MartinRusk/G1000/design/Panel/Gear handle.3mf

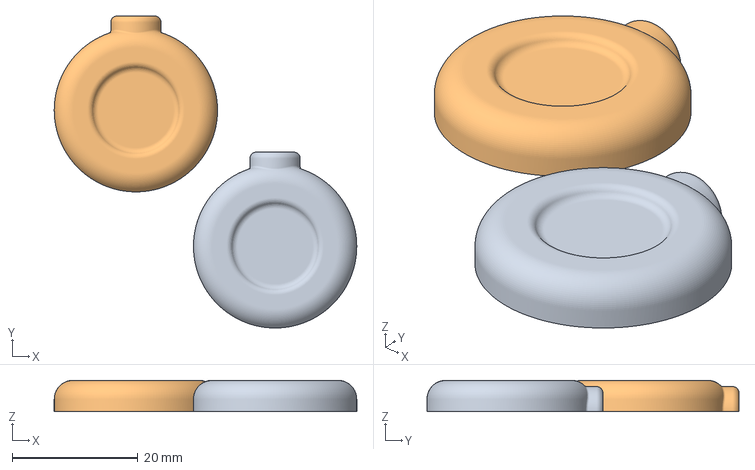
[picture p17: CAD file, 2022-03-11]
design/Panel/Gear handle.3mf
48.2 x 49.7 x 5.00 mm
Gear handle large left.stl
Gear handle large right.stl
