MartinRusk/G1000/design/Bezel/Bezel Top.3mf

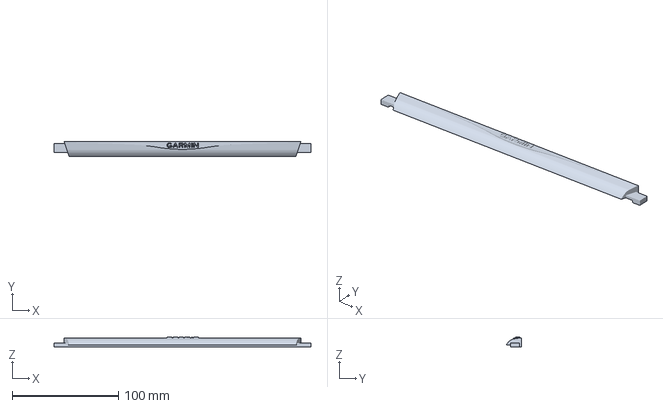
[picture p18: CAD file, 2022-01-23]
design/Bezel/Bezel Top.3mf
241.4 x 14.4 x 9.72 mm
