MartinRusk/G1000/design/Buttons/Buttons KEY.3mf

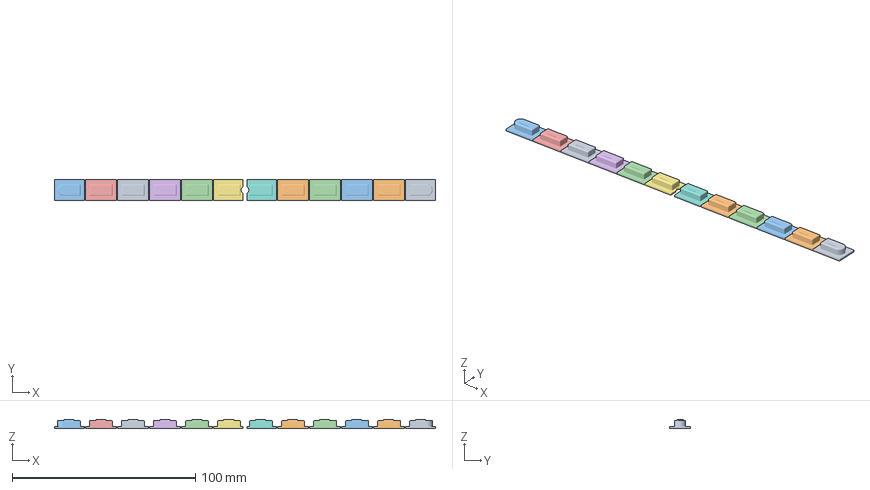
[picture p19: CAD file, 2022-01-23]
design/Buttons/Buttons KEY.3mf
208.1 x 11.6 x 4.67 mm
Buttons KEY_1
Buttons KEY_2
Buttons KEY_3
Buttons KEY_4
Buttons KEY_5
Buttons KEY_6
Buttons KEY_7
Buttons KEY_8
Buttons KEY_9
Buttons KEY_10
Buttons KEY_11
Buttons KEY_12
