MartinRusk/G1000/design/Buttons/STL/KEY 12.stl

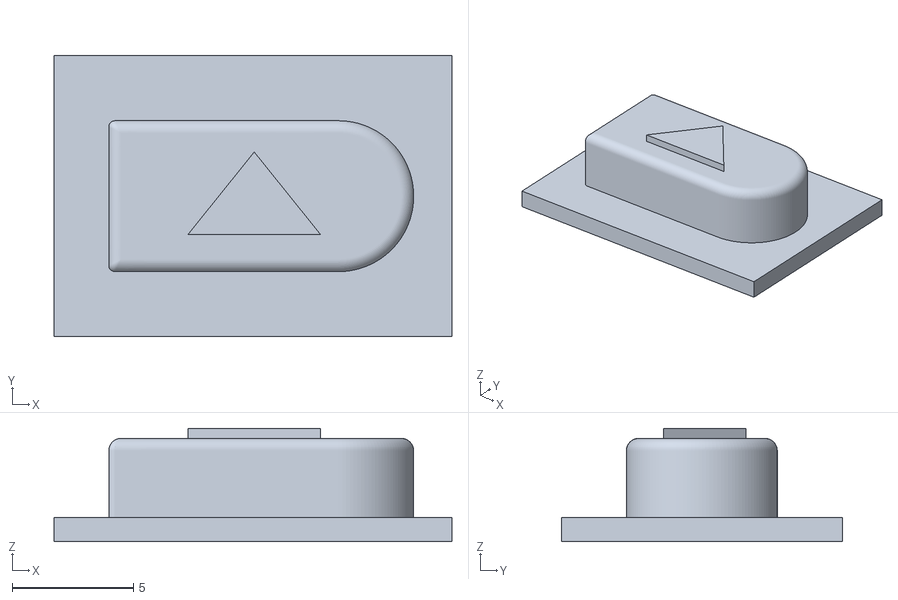
[picture p20: CAD file, 2022-04-21]
design/Buttons/STL/KEY 12.stl
16.4 x 11.6 x 4.67
