MartinRusk/G1000/design/Display/Display Frame VS104T.3mf

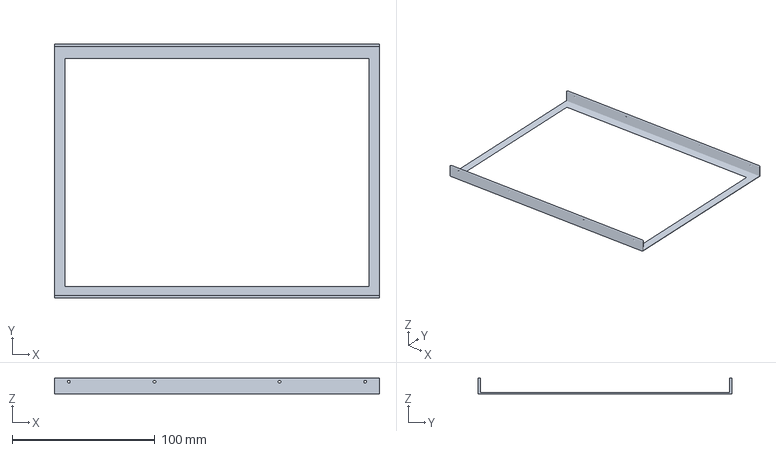
[picture p21: CAD file, 2022-01-28]
design/Display/Display Frame VS104T.3mf
227.6 x 177.7 x 11.0 mm
