MartinRusk/G1000/design/Encoders/Rudder Trim Knob.3mf

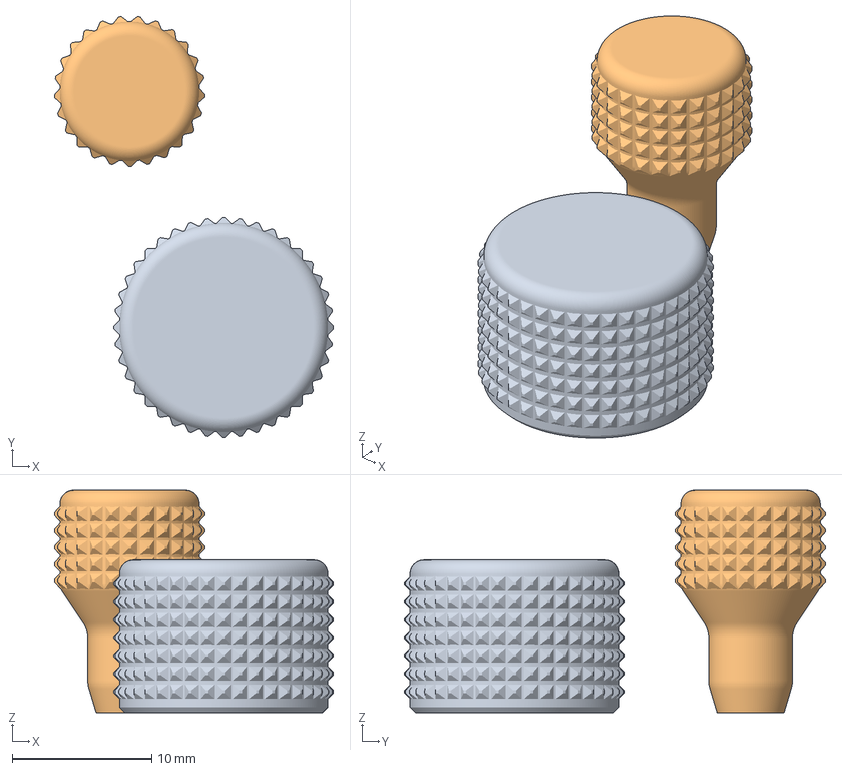
[picture p22: CAD file, 2022-03-11]
design/Encoders/Rudder Trim Knob.3mf
20.1 x 30.2 x 16.0 mm
Trim Knob knurled.stl
Range Pan Knob knurled new.stl
