MartinRusk/G1000/design/Encoders/STL/Encoder Tool.stl

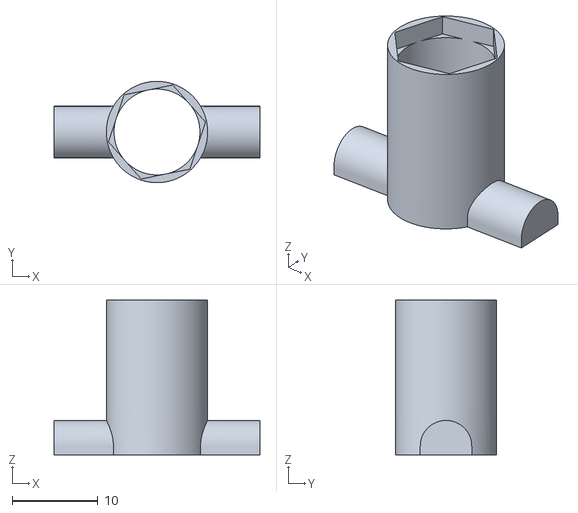
[picture p23: CAD file, 2022-04-21]
design/Encoders/STL/Encoder Tool.stl
24.0 x 11.8 x 18.0
