MartinRusk/G1000/design/Panel/Flap handle.3mf

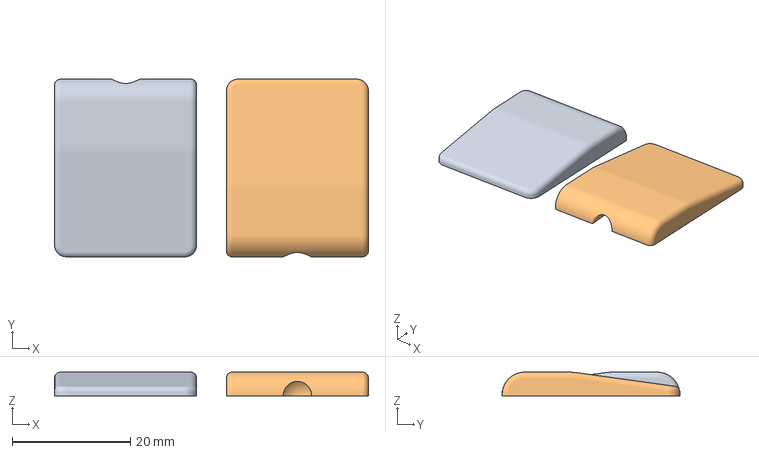
[picture p24: CAD file, 2022-03-11]
design/Panel/Flap handle.3mf
53.0 x 30.0 x 4.00 mm
Flap Selector lower.stl
Flap Selector upper.stl
