MartinRusk/G1000/design/Bezel/Bezel SD Card.3mf

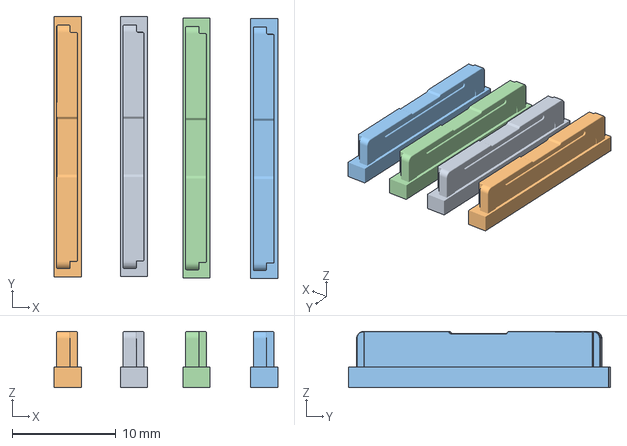
[picture p25: CAD file, 2022-01-23]
design/Bezel/Bezel SD Card.3mf
21.6 x 25.3 x 5.42 mm
