MartinRusk/G1000/design/Buttons/STL/APR.stl

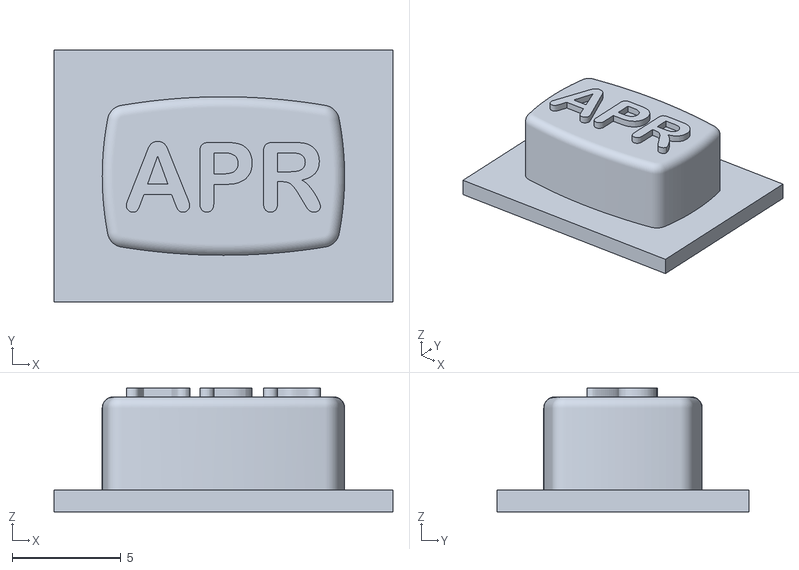
[picture p26: CAD file, 2022-04-21]
design/Buttons/STL/APR.stl
15.6 x 11.6 x 5.69
