MartinRusk/G1000/design/Display/Display Bracket VS104T.3mf

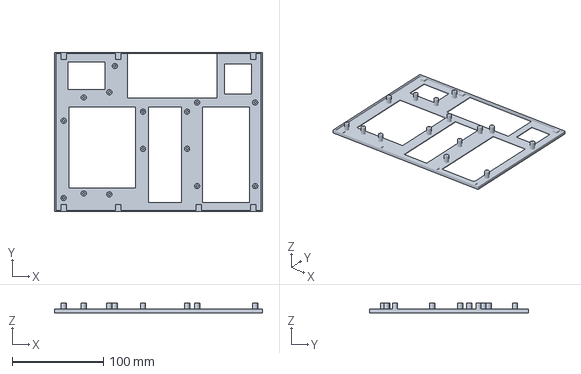
[picture p27: CAD file, 2022-01-28]
design/Display/Display Bracket VS104T.3mf
227.6 x 174.5 x 10.6 mm
