MartinRusk/G1000/design/Encoders/Encoder Knobs.3mf

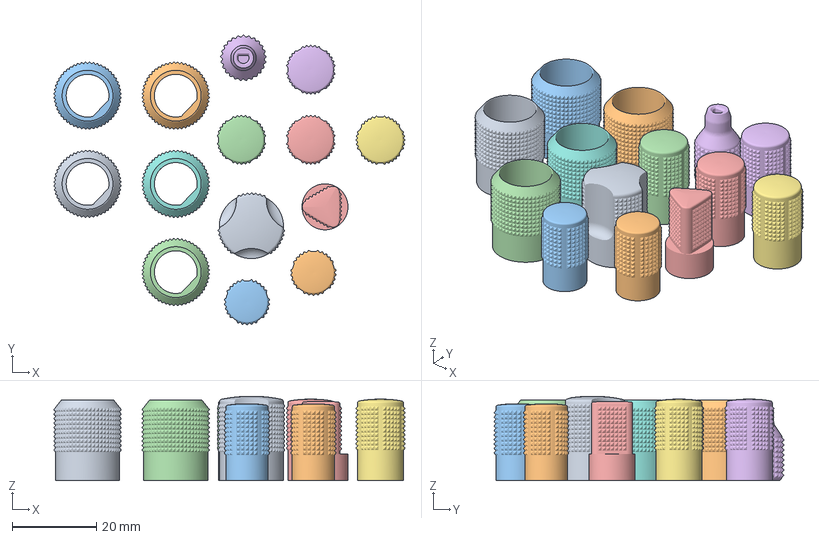
[picture p28: CAD file, 2022-02-15]
design/Encoders/Encoder Knobs.3mf
83.2 x 68.7 x 20.0 mm
HDG knob knurled 6mm round shaft.stl
Volume knob knurled 6mm round shaft.stl
Dual Inner FMS Knob knurled FSM shaft.stl
Dual Outer Knob knurled FSM shaft.stl
Dual Inner CRS Knob knurled FSM shaft.stl
Range Pan Knob knurled new long.stl
