MartinRusk/G1000/design/Encoders/STL/Encoder Inner Shaft.stl

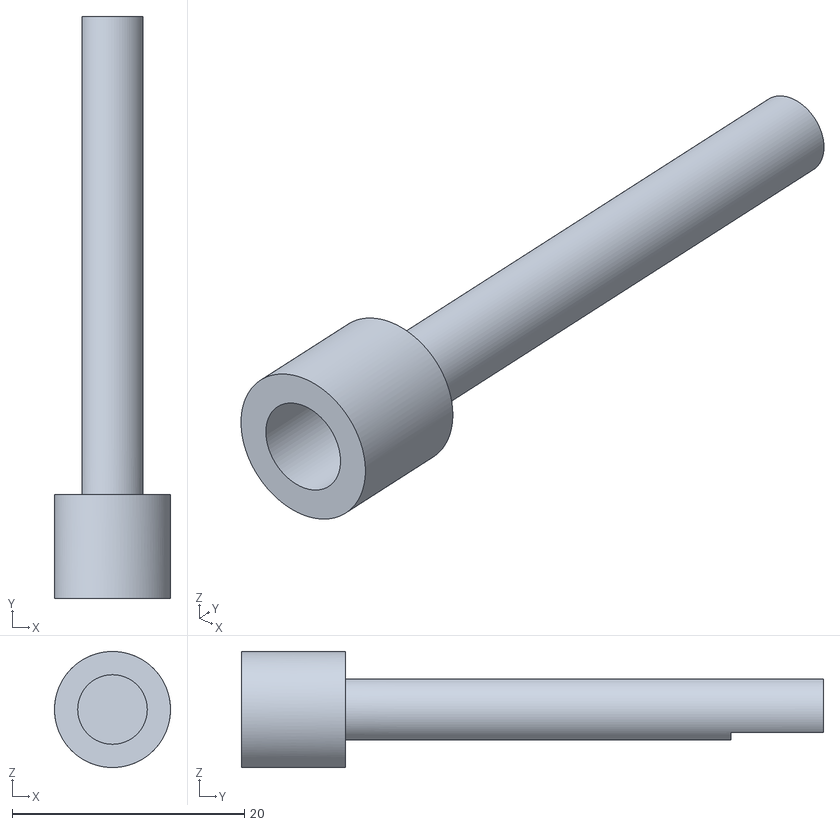
[picture p29: CAD file, 2022-04-21]
design/Encoders/STL/Encoder Inner Shaft.stl
10.0 x 50.2 x 10.0
