MartinRusk/G1000/design/Bezel/Bezel Right.3mf

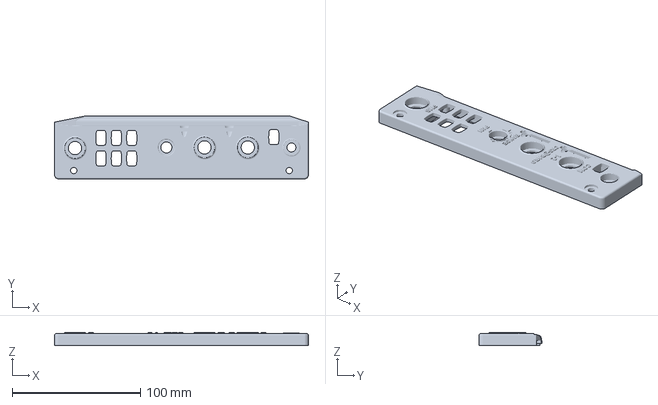
[picture p31: CAD file, 2022-01-23]
design/Bezel/Bezel Right.3mf
198.0 x 49.0 x 10.4 mm
