MartinRusk/G1000/design/Encoders/Encoder Lids.3mf

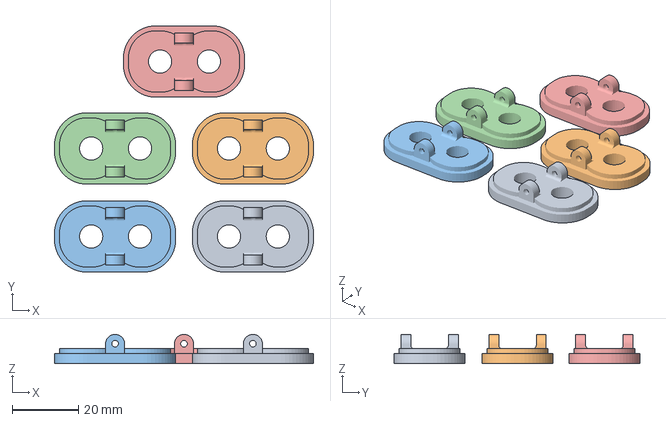
[picture p32: CAD file, 2022-01-23]
design/Encoders/Encoder Lids.3mf
78.0 x 74.2 x 8.80 mm
