MartinRusk/G1000/design/Encoders/STL/Encoder Gear.stl

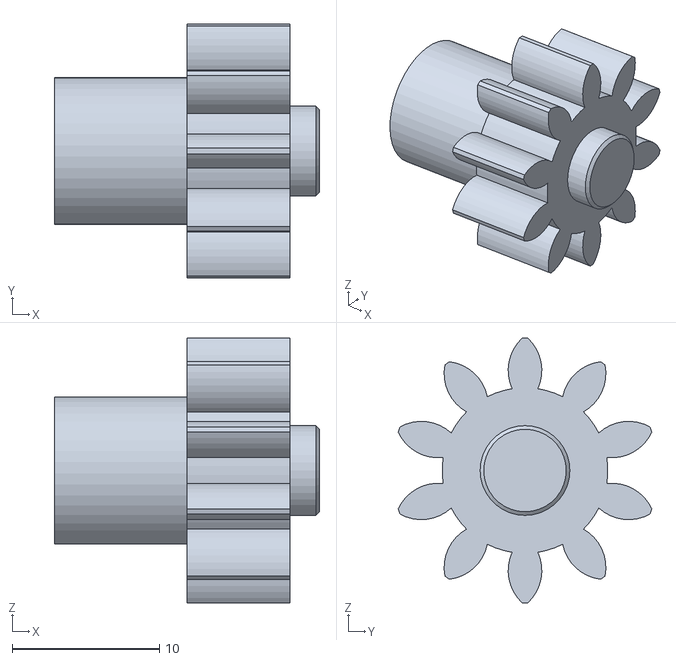
[picture p33: CAD file, 2022-04-21]
design/Encoders/STL/Encoder Gear.stl
18.0 x 17.2 x 18.0
