MartinRusk/G1000/design/Housing/Back cover center.3mf

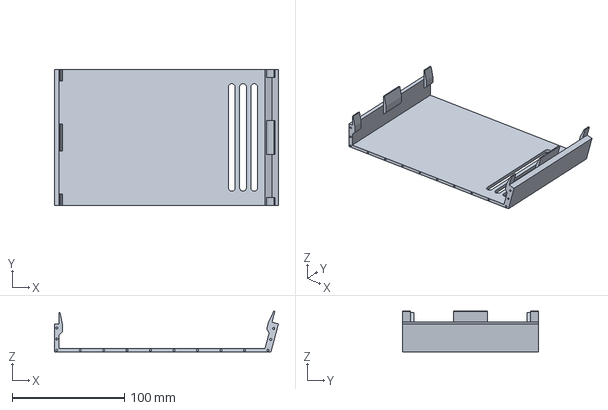
[picture p34: CAD file, 2022-10-27]
design/Housing/Back cover center.3mf
200.0 x 121.0 x 36.5 mm
