MartinRusk/G1000/design/Panel/Panel Right.3mf

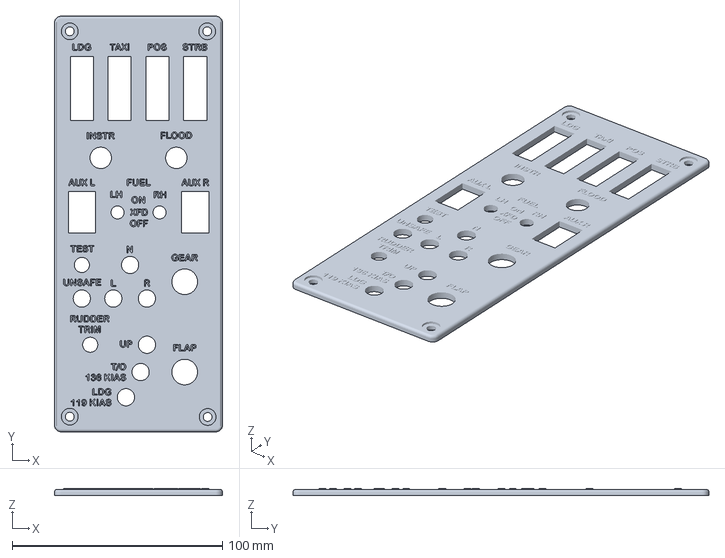
[picture p35: CAD file, 2022-02-15]
design/Panel/Panel Right.3mf
80.0 x 198.0 x 3.40 mm
