MartinRusk/G1000/design/Bezel/Bezel Bottom.3mf

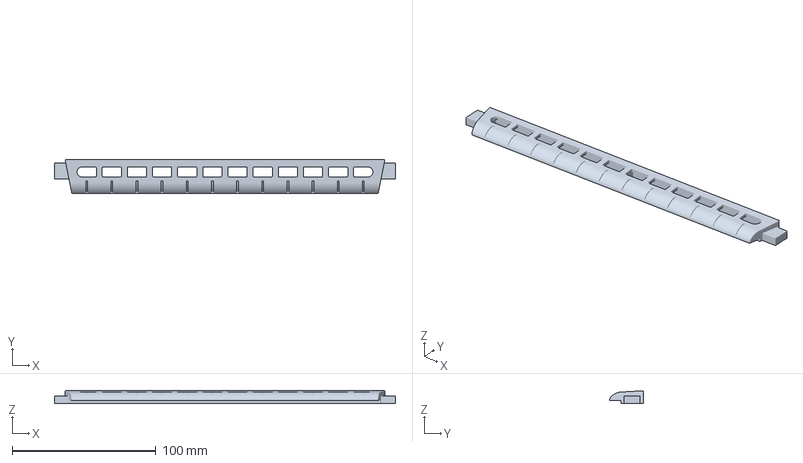
[picture p36: CAD file, 2022-01-23]
design/Bezel/Bezel Bottom.3mf
237.1 x 23.6 x 8.73 mm
