MartinRusk/G1000/design/Buttons/STL/BC.stl

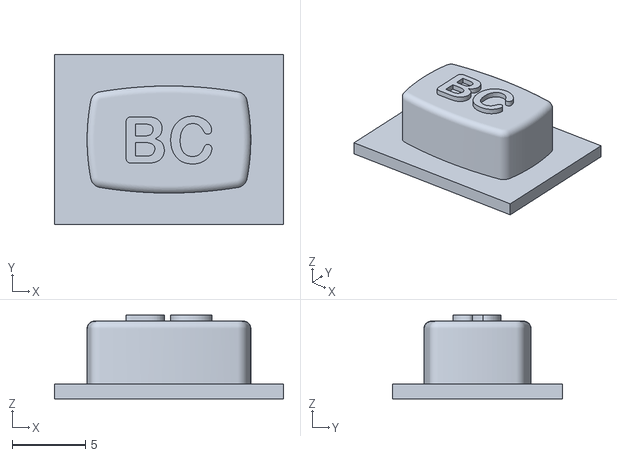
[picture p37: CAD file, 2022-04-21]
design/Buttons/STL/BC.stl
15.6 x 11.6 x 5.69
