MartinRusk/G1000/design/Encoders/Encoder Housings.3mf

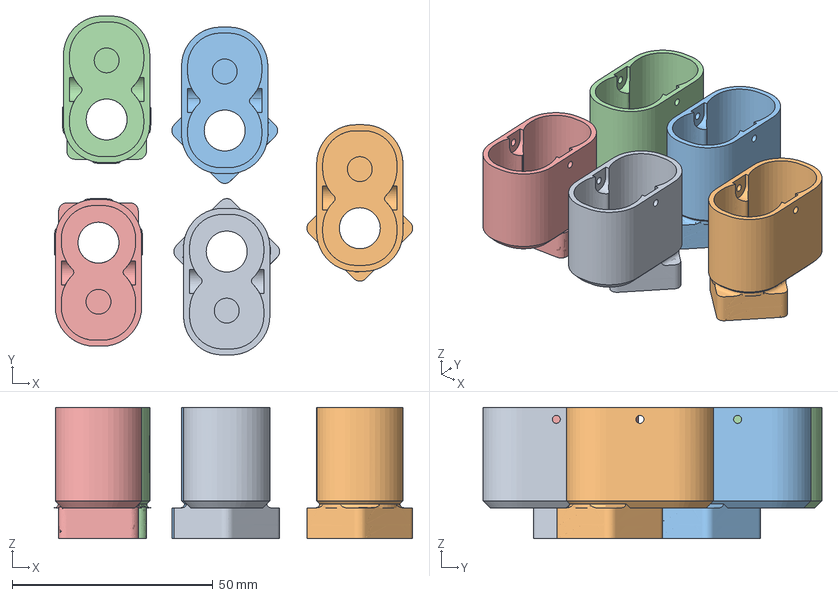
[picture p38: CAD file, 2022-01-23]
design/Encoders/Encoder Housings.3mf
89.2 x 84.3 x 32.7 mm
HousingV2-deeper=45-NXi.stl
HousingV2-deeper-90-NXi.stl
