MartinRusk/G1000/design/Encoders/STL/Encoder Knob Volume.stl

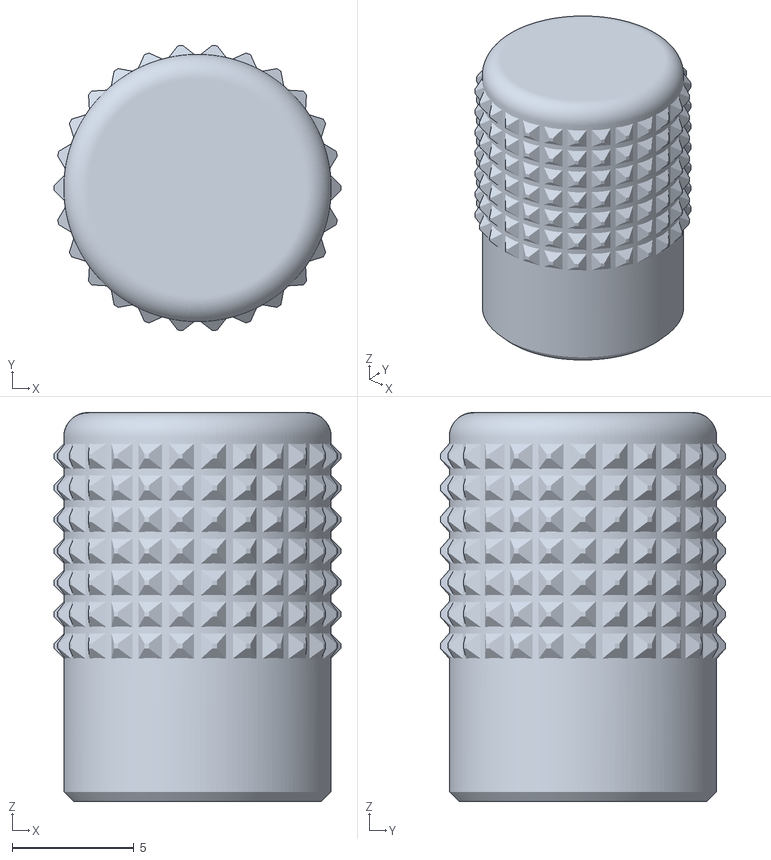
[picture p39: CAD file, 2022-04-21]
design/Encoders/STL/Encoder Knob Volume.stl
11.8 x 11.7 x 16.0
