MartinRusk/G1000/design/Housing/Backcover Panel.3mf

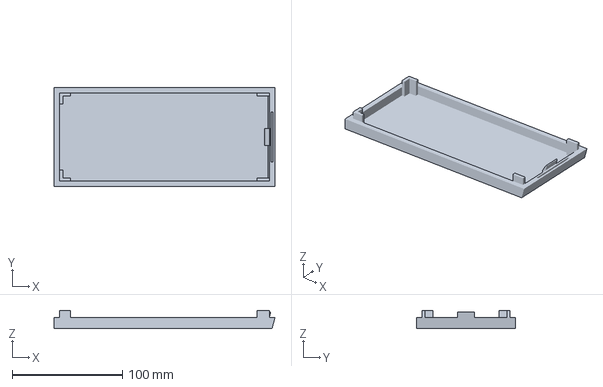
[picture p40: CAD file, 2022-03-11]
design/Housing/Backcover Panel.3mf
200.0 x 90.0 x 16.6 mm
