MartinRusk/G1000/design/Buttons/STL/KEY 6.stl

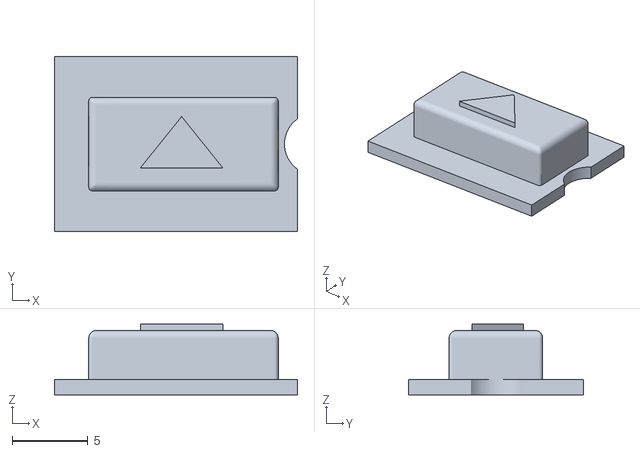
[picture p41: CAD file, 2022-04-21]
design/Buttons/STL/KEY 6.stl
16.1 x 11.6 x 4.67
