MartinRusk/G1000/design/Encoders/Encoder Gears.3mf

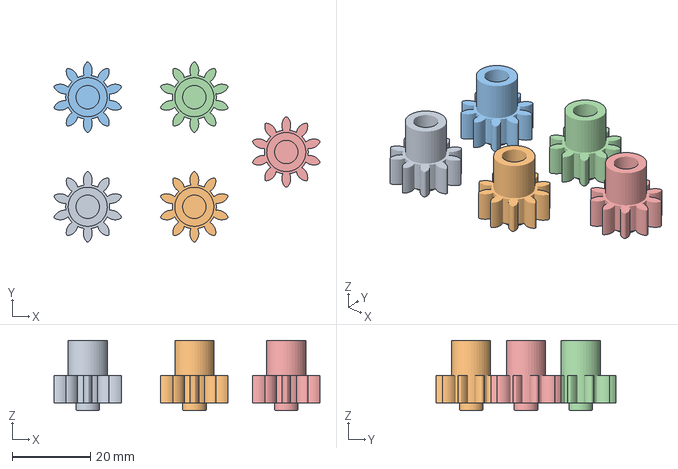
[picture p42: CAD file, 2022-01-23]
design/Encoders/Encoder Gears.3mf
68.0 x 46.0 x 18.0 mm
