MartinRusk/G1000/design/Encoders/STL/Encoder Knob Dual Outer.stl

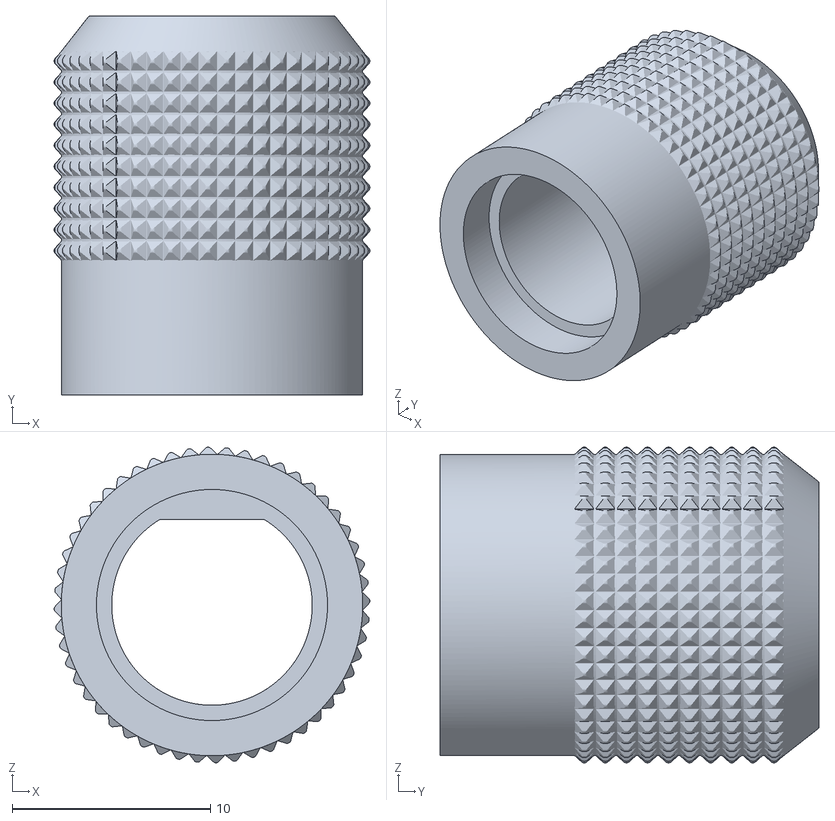
[picture p43: CAD file, 2022-04-21]
design/Encoders/STL/Encoder Knob Dual Outer.stl
15.9 x 19.1 x 15.9
