MartinRusk/G1000/design/Housing/Housing Panel.3mf

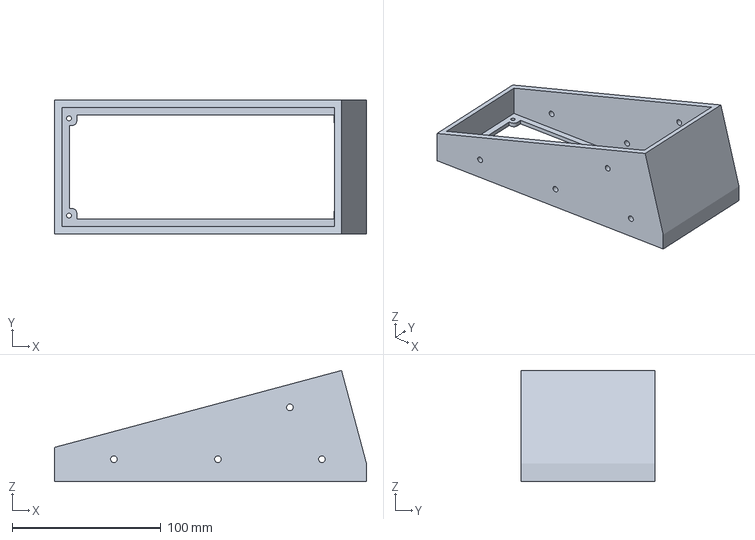
[picture p44: CAD file, 2022-02-15]
design/Housing/Housing Panel.3mf
210.0 x 90.0 x 74.7 mm
