MartinRusk/G1000/design/Buttons/STL/Blank.stl

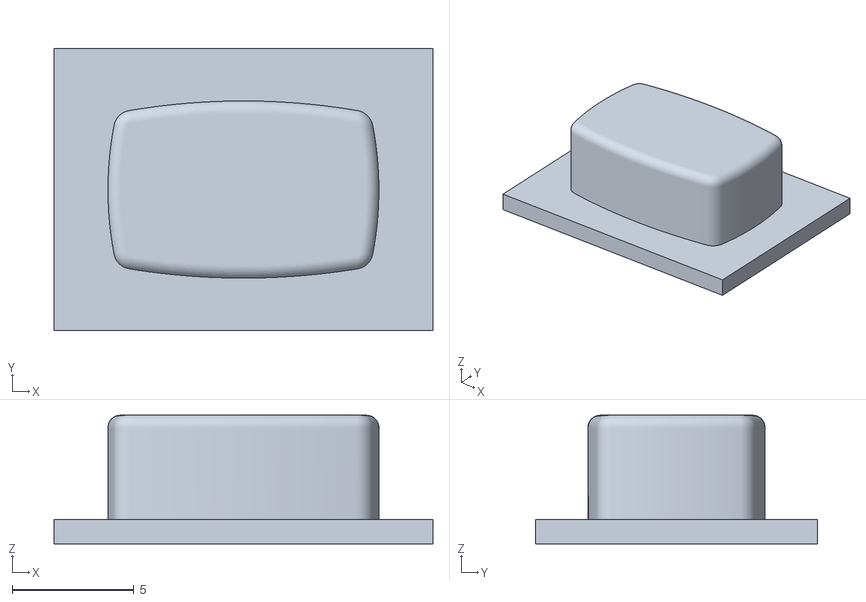
[picture p45: CAD file, 2022-04-21]
design/Buttons/STL/Blank.stl
15.6 x 11.6 x 5.29
