MartinRusk/G1000/design/Encoders/Encoder Inner Shafts.3mf

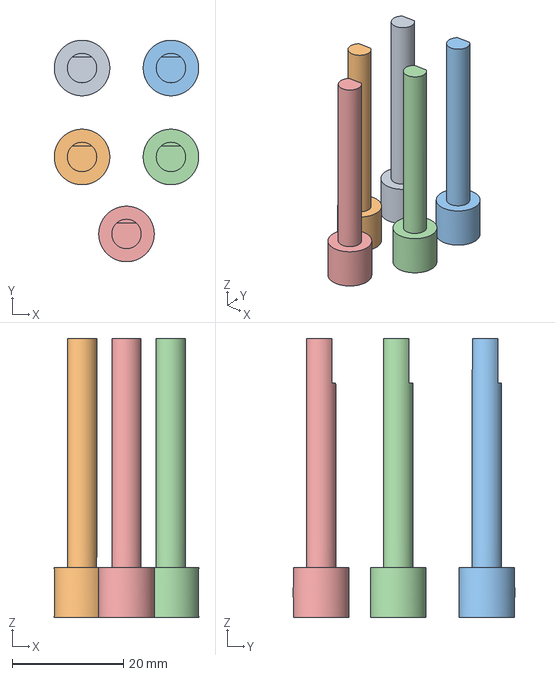
[picture p46: CAD file, 2022-01-23]
design/Encoders/Encoder Inner Shafts.3mf
26.0 x 39.9 x 50.2 mm
