MartinRusk/G1000/design/Encoders/STL/Encoder Housing 45°.stl

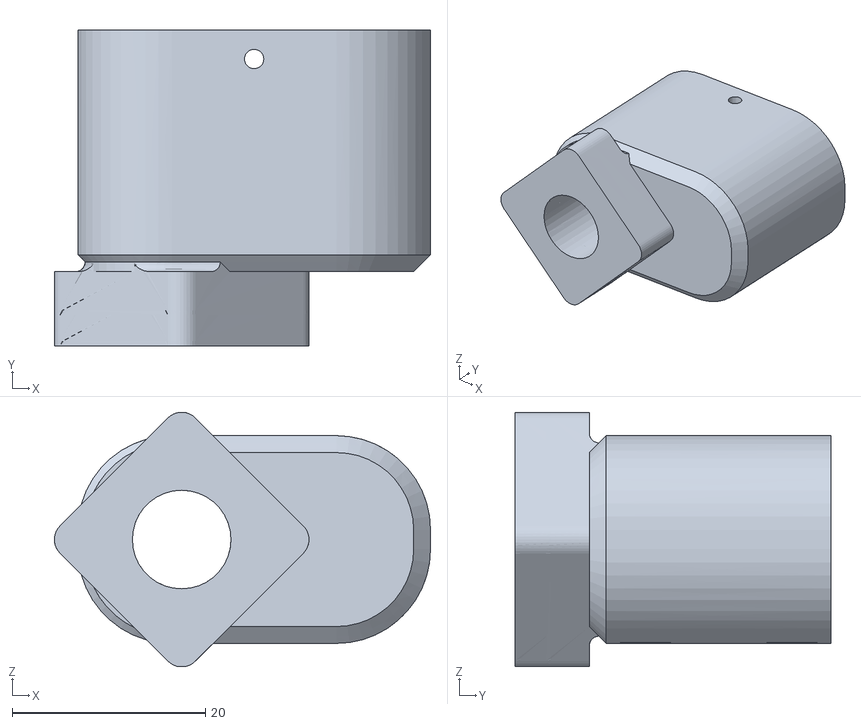
[picture p47: CAD file, 2022-04-21]
design/Encoders/STL/Encoder Housing 45°.stl
38.9 x 32.7 x 26.3
