MartinRusk/G1000/design/Housing/Housing Front.3mf

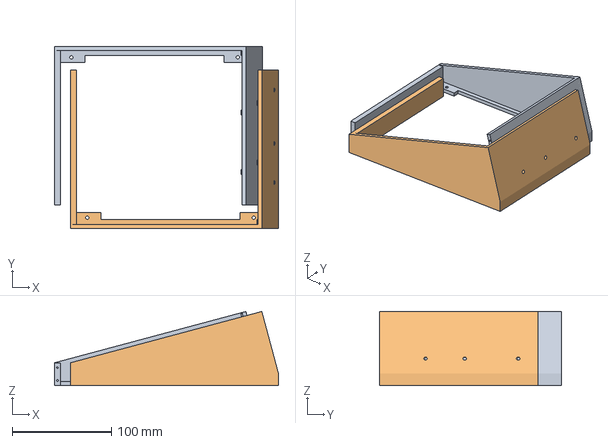
[picture p48: CAD file, 2022-01-28]
design/Housing/Housing Front.3mf
226.1 x 183.8 x 74.8 mm
10-L-v2.stl
10-R-v2.stl
