MartinRusk/G1000/design/Encoders/Encoder Outer Shafts.3mf

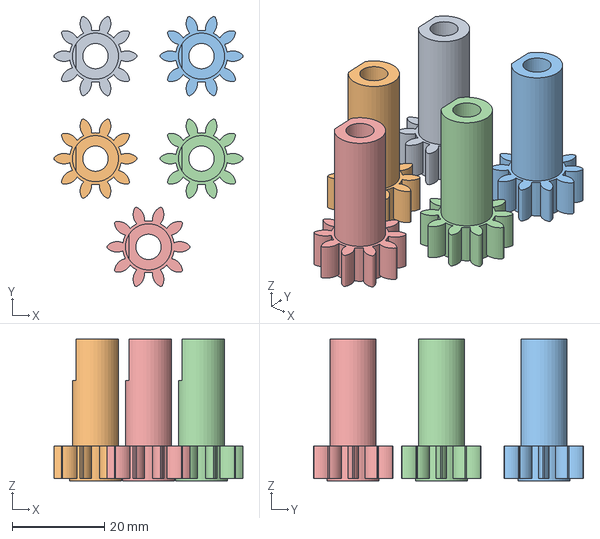
[picture p49: CAD file, 2022-01-23]
design/Encoders/Encoder Outer Shafts.3mf
41.0 x 58.6 x 30.7 mm
