MartinRusk/G1000/design/Encoders/STL/Encoder Outer Shaft.stl

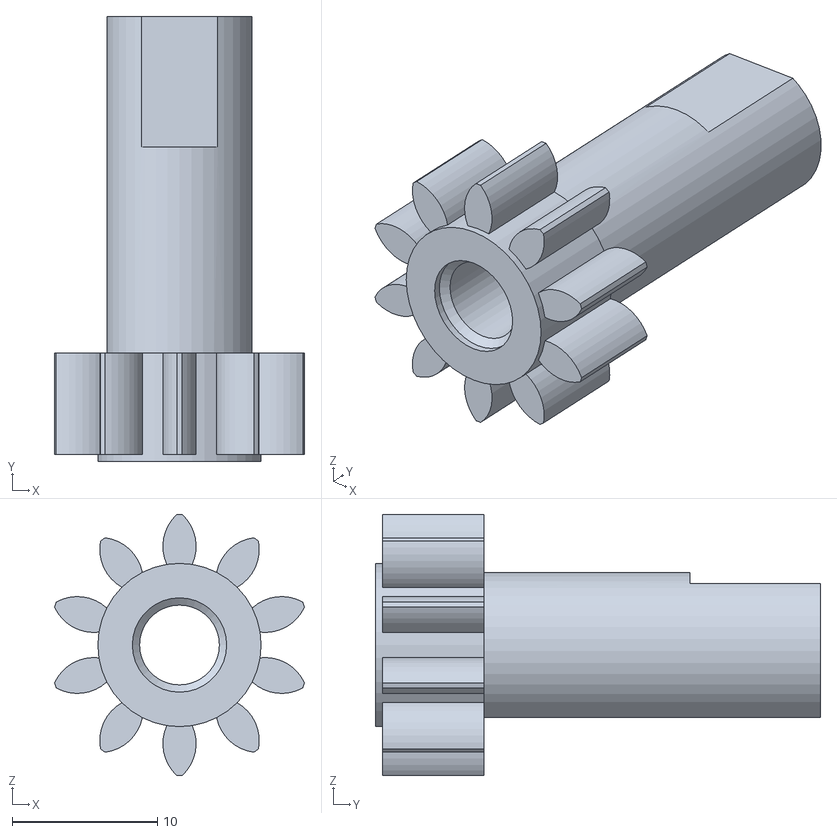
[picture p50: CAD file, 2022-04-21]
design/Encoders/STL/Encoder Outer Shaft.stl
17.2 x 30.7 x 18.0
