MartinRusk/G1000/design/Encoders/STL/Encoder Knob HDG.stl

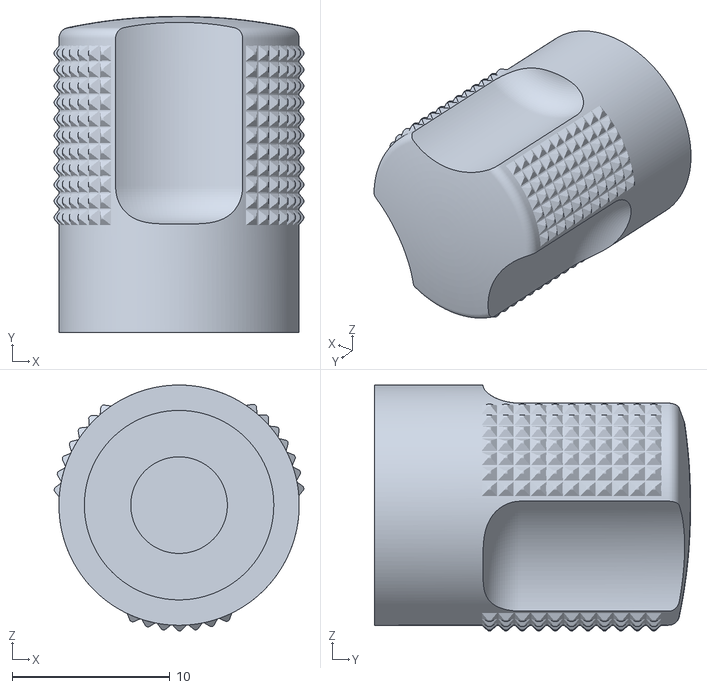
[picture p51: CAD file, 2022-04-21]
design/Encoders/STL/Encoder Knob HDG.stl
15.8 x 20.0 x 15.6
