MartinRusk/G1000/design/Encoders/STL/Encoder Lid.stl

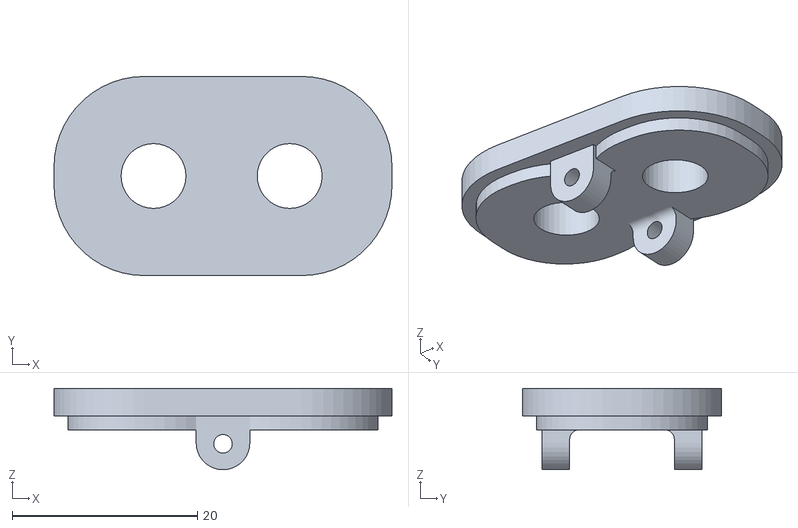
[picture p52: CAD file, 2022-04-21]
design/Encoders/STL/Encoder Lid.stl
36.5 x 21.5 x 8.80
