MartinRusk/G1000/design/Encoders/STL/Range Pan Knob.stl

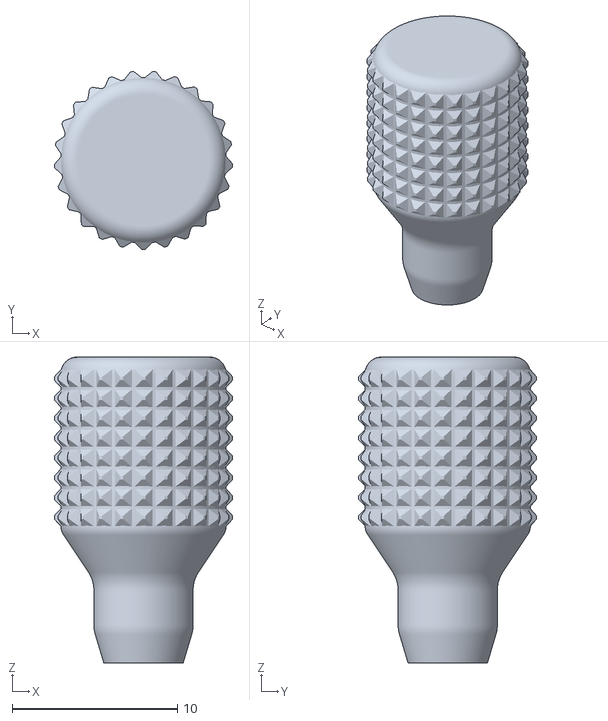
[picture p53: CAD file, 2022-04-21]
design/Encoders/STL/Range Pan Knob.stl
10.8 x 10.8 x 18.5
