MartinRusk/G1000/design/Encoders/STL/Encoder Housing 90°.stl

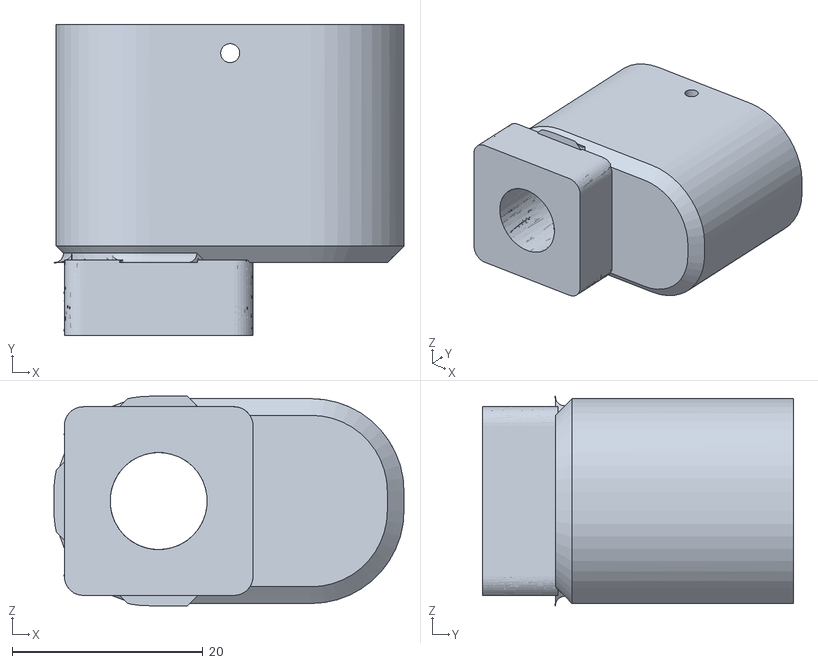
[picture p54: CAD file, 2022-04-21]
design/Encoders/STL/Encoder Housing 90°.stl
36.7 x 32.6 x 22.0
