MartinRusk/G1000/design/Buttons/STL/FFL.stl

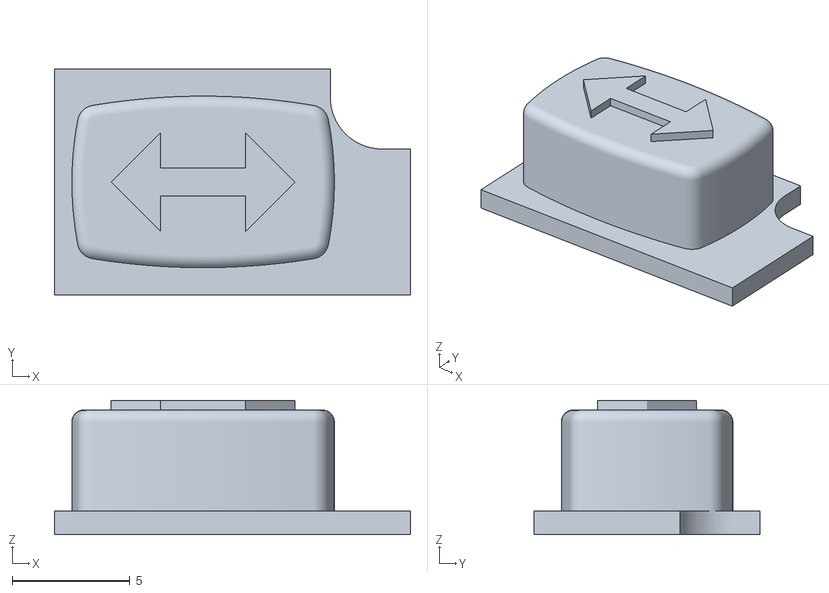
[picture p55: CAD file, 2022-04-21]
design/Buttons/STL/FFL.stl
15.1 x 9.60 x 5.68
