MartinRusk/G1000/hardware/Schematic/Schematic_G1000_Softkey.pdf

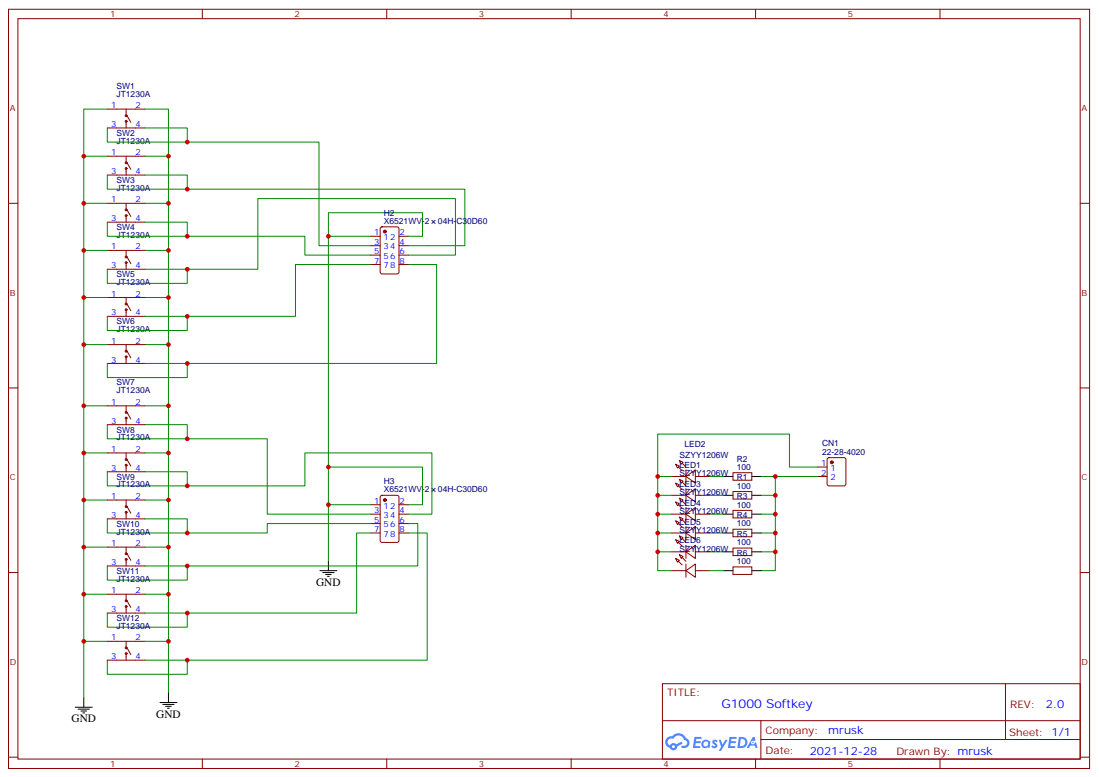
[picture p72: page 1]
